gugray/SolarLCD/code/board/src/animations_euclidean.cpp

#include <Arduino.h>
#include "animations.h"
#include "euclidean.h"
#include "globals.h"

#define FLAG_SETUP 1

/* AnimState usage
   counter: frame count
   a: current count in 16-beat bar
   b: scaler (beat at every 'scaler'-th frame)
   c: bars played
   d:
   mem:
      [0..3]: Current value per track (0, 1, 2)
      [4..27]: Track definitions, 6 bytes per track
               Each 6 bytes: rhythm 1 and optional rhythm 2
               [nBeats, offset, volume], [nBeats, offset, volume]
*/

void setupEuclideanO()
{
  as.b = random(5, 11);

  uint8_t nVoices = random(4, 6);
  for (uint8_t i = 0; i < nVoices; ++i)
  {
    uint8_t trackIx = i % 4;
    uint8_t nBeats = random(1, 6);
    uint8_t *ptr = as.mem + 4 + 6 * trackIx;
    if (*ptr != 0)
      ptr += 3;
    *ptr = nBeats;
    *(ptr + 1) = random(0, 16 / nBeats); // offset
    *(ptr + 2) = random(1, 3);           // volume
  }
}

uint8_t getVolumeO(uint8_t *ptr)
{
  uint8_t nBeats = *ptr;
  if (nBeats == 0)
    return 0;
  uint8_t offset = *(ptr + 1);
  uint8_t volume = *(ptr + 2);
  if (isOnBeat(nBeats, offset, as.a))
    return volume;
  else
    return 0;
}

void beatEuclideanO()
{
  for (uint8_t i = 0; i < 4; ++i)
  {
    uint8_t val = *(as.mem + i);
    if (val > 0)
      --val;
    val += getVolumeO(as.mem + 4 + i * 6);
    val += getVolumeO(as.mem + 4 + i * 6 + 3);
    if (val > 2)
      val = 2;
    *(as.mem + i) = val;
  }
  ++as.a;
  if (as.a == 16)
  {
    as.a = 0;
    ++as.c;
  }
}

/* AnimState usage
   counter: frame count
   a: current count in 16-beat bar
   b: scaler (beat at every 'scaler'-th frame)
   c: bars played
   d:
   mem:
      [0..3]: Current value per track (0 or 1)
      [4..11]: Track definitions, 2 bytes per track
               [nBeats, offset]
*/

void setupEuclideanU()
{
  as.b = random(6, 11);

  for (uint8_t trackIx = 0; trackIx < 4; ++trackIx)
  {
    uint8_t nBeats = random(4, 7);
    uint8_t *ptr = as.mem + 4 + 2 * trackIx;
    *ptr = nBeats;
    *(ptr + 1) = random(0, 16 / nBeats); // offset
  }
}

void beatEuclideanU()
{
  for (uint8_t i = 0; i < 4; ++i)
  {
    uint8_t *ptr = as.mem + 4 + 2 * i;
    uint8_t nBeats = *ptr;
    uint8_t offset = *(ptr + 1);
    if (isOnBeat(nBeats, offset, as.a))
      *(as.mem + i) = 1;
    else
      *(as.mem + i) = 0;
  }
  ++as.a;
  if (as.a == 16)
  {
    as.a = 0;
    ++as.c;
  }
}

bool animEuclidean(bool varO)
{
  // Setup once
  if (!as.getFlag(FLAG_SETUP))
  {
    if (varO)
      setupEuclideanO();
    else
      setupEuclideanU();
    as.setFlag(FLAG_SETUP, true);
  }

  if ((as.counter++ % as.b) != 0)
    return false;

  // Update value of each track
  if (varO)
    beatEuclideanO();
  else
    beatEuclideanU();

  // If we're done, return here, before flashing up last screen for 1 frame
  // Play 8 bars
  if (as.c >= 8)
    return true;

  // Visualize
  ht1621.clearBuffer();
  for (uint8_t i = 0; i < 4; ++i)
  {
    uint8_t val = *(as.mem + i);
    if (varO)
    {
      painter.setSegs(i, SG_BM);
      if (val >= 1)
        painter.setSegs(i, SG_MD | SG_BL | SG_BR);
      if (val >= 2)
        painter.setSegs(i, SG_TP | SG_TL | SG_TR);
    }
    else
    {
      if (val != 0)
        painter.setSegs(i, SG_BL | SG_BR | SG_BM);
      uint8_t eighths = (as.a / 2) % 8;
      bool left = (eighths % 2) == 0;
      painter.setSegIx(eighths / 2, 0);
      painter.setSegIx(eighths / 2, left ? 1 : 2);
    }
  }
  ht1621.wrBuffer();

  return false;
}

bool animEuclideanO(bool fast)
{
  return animEuclidean(true);
}

bool animEuclideanU(bool fast)
{
  return animEuclidean(false);
}
