gugray/SolarLCD/code/board/src/blink_seq.h

#ifndef BLINK_SEQ_H
#define BLINK_SEQ_H

// Initializes a new rand blink sequence
void initBlinkSeq();

// Performs a blink sequence and returns number of half-seconds elapsed
uint16_t blinkOneSeq();

#endif
